amadeuspzs/esp8266-temperature-humidity/analysis/measure-current/mcp-dht.csv

timestamp | current | voltage
52106 | -3.75 | 4176.25
52109 | -2.50 | 4177.50
52111 | -2.50 | 4176.25
52113 | -3.75 | 4176.25
52115 | -5.00 | 4176.25
52117 | -3.75 | 4176.25
52119 | -2.50 | 4176.25
52122 | -3.75 | 4176.25
52124 | -1.25 | 4177.50
52126 | -5.00 | 4176.25
52128 | -3.75 | 4176.25
52130 | -2.50 | 4176.25
52132 | -3.75 | 4176.25
52134 | -3.75 | 4176.25
52137 | -3.75 | 4176.25
52140 | -1.25 | 4176.25
52142 | -3.75 | 4177.50
52144 | -3.75 | 4176.25
52146 | -3.75 | 4176.25
52148 | -5.00 | 4176.25
52151 | -3.75 | 4176.25
52153 | -3.75 | 4176.25
52155 | -3.75 | 4176.25
52157 | -2.50 | 4176.25
52159 | -5.00 | 4176.25
52161 | -3.75 | 4176.25
52164 | -3.75 | 4176.25
52166 | -3.75 | 4177.50
52168 | -3.75 | 4176.25
52170 | -2.50 | 4176.25
52172 | -2.50 | 4175.00
52174 | -2.50 | 4176.25
52177 | -3.75 | 4177.50
52179 | -3.75 | 4175.00
52182 | -3.75 | 4176.25
52184 | -3.75 | 4176.25
52186 | -3.75 | 4176.25
52188 | -2.50 | 4176.25
52190 | -3.75 | 4176.25
52193 | -3.75 | 4176.25
52195 | -3.75 | 4176.25
52197 | -3.75 | 4176.25
52199 | -3.75 | 4176.25
52201 | -5.00 | 4176.25
52203 | -3.75 | 4176.25
52206 | -3.75 | 4176.25
52208 | -3.75 | 4176.25
52210 | -3.75 | 4176.25
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
