amadeuspzs/esp8266-temperature-humidity/analysis/measure-current/mcp-si.csv

timestamp | current | voltage
215763 | -3.75 | 4178.75
215766 | -2.50 | 4178.75
215768 | -3.75 | 4178.75
215770 | -2.50 | 4180.00
215772 | -3.75 | 4178.75
215775 | -2.50 | 4180.00
215777 | -2.50 | 4178.75
215779 | -5.00 | 4178.75
215781 | -3.75 | 4178.75
215783 | -2.50 | 4178.75
215786 | -3.75 | 4178.75
215788 | -2.50 | 4180.00
215790 | -2.50 | 4178.75
215792 | -3.75 | 4180.00
215794 | -3.75 | 4178.75
215797 | -2.50 | 4178.75
215799 | -2.50 | 4178.75
215801 | -2.50 | 4178.75
215803 | -2.50 | 4178.75
215805 | -3.75 | 4178.75
215809 | -3.75 | 4180.00
215811 | -3.75 | 4178.75
215813 | -3.75 | 4178.75
215815 | -3.75 | 4178.75
215817 | -2.50 | 4178.75
215820 | -3.75 | 4180.00
215822 | -3.75 | 4180.00
215824 | -3.75 | 4178.75
215826 | -3.75 | 4178.75
215828 | -2.50 | 4180.00
215831 | -3.75 | 4177.50
215833 | -3.75 | 4178.75
215835 | -3.75 | 4180.00
215837 | -3.75 | 4178.75
215839 | -2.50 | 4178.75
215842 | -2.50 | 4178.75
215844 | -2.50 | 4178.75
215846 | -2.50 | 4178.75
215848 | -2.50 | 4178.75
215851 | -2.50 | 4181.25
215853 | -2.50 | 4180.00
215856 | -2.50 | 4180.00
215858 | -3.75 | 4178.75
215860 | -2.50 | 4178.75
215862 | -3.75 | 4178.75
215864 | -2.50 | 4177.50
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
