amadeuspzs/esp8266-temperature-humidity/analysis/measure-current/slow-auto.csv

Timestamp | Amps
2021-02-22 15:51:02.764359 | 5.64e-09
2021-02-22 15:51:02.764908 | 2.01e-09
2021-02-22 15:51:02.765551 | 5.24e-09
2021-02-22 15:51:02.766239 | 4.84e-09
2021-02-22 15:51:02.766950 | 3.63e-09
2021-02-22 15:51:02.767742 | 4.03e-09
2021-02-22 15:51:02.768414 | 4.84e-09
2021-02-22 15:51:02.769081 | -5.24e-09
2021-02-22 15:51:02.769889 | 2.42e-09
2021-02-22 15:51:02.770635 | 5.64e-09
2021-02-22 15:51:02.771264 | -2.82e-09
2021-02-22 15:51:02.771958 | 2.42e-09
2021-02-22 15:51:02.772755 | 7.25e-09
2021-02-22 15:51:02.773476 | -8.1e-10
2021-02-22 15:51:02.774299 | 1.21e-09
2021-02-22 15:51:02.774881 | 4.43e-09
2021-02-22 15:51:02.775707 | -5.64e-09
2021-02-22 15:51:02.776488 | -8.1e-10
2021-02-22 15:51:02.777055 | 6.04e-09
2021-02-22 15:51:02.777880 | -4.03e-09
2021-02-22 15:51:02.778717 | 8.1e-10
2021-02-22 15:51:02.779432 | 3.63e-09
2021-02-22 15:51:02.780113 | -5.64e-09
2021-02-22 15:51:02.780817 | 5.24e-09
2021-02-22 15:51:02.781465 | 4.03e-09
2021-02-22 15:51:02.782227 | -1.007e-08
2021-02-22 15:51:02.782843 | 3.63e-09
2021-02-22 15:51:02.783751 | 5.24e-09
2021-02-22 15:51:02.784434 | 0.0
2021-02-22 15:51:02.785156 | 3.22e-09
2021-02-22 15:51:02.785728 | 4.84e-09
2021-02-22 15:51:02.786615 | 1.61e-09
2021-02-22 15:51:02.787189 | 5.64e-09
2021-02-22 15:51:02.788029 | 2.42e-09
2021-02-22 15:51:02.788733 | 6.04e-09
2021-02-22 15:51:02.789595 | 0.0
2021-02-22 15:51:02.790233 | 3.22e-09
2021-02-22 15:51:02.791114 | 6.85e-09
2021-02-22 15:51:02.791765 | -4.03e-09
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
2021-02-22 15:51:05.323331 | 0.01491
2021-02-22 15:51:05.324135 | 0.01531
2021-02-22 15:51:05.324833 | 0.01491
2021-02-22 15:51:05.325532 | 0.01491
2021-02-22 15:51:05.326939 | 0.01531
2021-02-22 15:51:05.327389 | 0.01531
2021-02-22 15:51:05.327843 | 0.01531
2021-02-22 15:51:05.328744 | 0.01491
2021-02-22 15:51:05.329244 | 0.01451
2021-02-22 15:51:05.330108 | 0.01491
2021-02-22 15:51:05.330731 | 0.01652
2021-02-22 15:51:05.331535 | 0.02136
2021-02-22 15:51:05.332164 | 0.03707
2021-02-22 15:51:05.333027 | 0.03828
2021-02-22 15:51:05.333577 | 0.04916
2021-02-22 15:51:05.334411 | 0.07374
2021-02-22 15:51:05.335176 | 0.0681
2021-02-22 15:51:05.335839 | 0.07253
2021-02-22 15:51:05.336707 | 0.07333
2021-02-22 15:51:05.337392 | 0.07535
2021-02-22 15:51:05.338033 | 0.07132
2021-02-22 15:51:05.338779 | 0.34773
2021-02-22 15:51:05.339694 | 0.06729
2021-02-22 15:51:05.340247 | 0.06689
2021-02-22 15:51:05.341001 | 0.06366
2021-02-22 15:51:05.341767 | 0.06568
2021-02-22 15:51:05.342472 | 0.06769
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
