amadeuspzs/esp8266-temperature-humidity/analysis/measure-current/slow-ma.csv

Timestamp | Amps
2021-02-22 15:52:27.855331 | 0.0004
2021-02-22 15:52:27.856332 | -0.0004
2021-02-22 15:52:27.856702 | 0.0
2021-02-22 15:52:27.857150 | 0.0004
2021-02-22 15:52:27.857979 | -0.0004
2021-02-22 15:52:27.858691 | -0.0004
2021-02-22 15:52:27.859492 | 0.0
2021-02-22 15:52:27.860437 | -0.00081
2021-02-22 15:52:27.860955 | -0.0004
2021-02-22 15:52:27.862128 | 0.0
2021-02-22 15:52:27.862557 | 0.0
2021-02-22 15:52:27.863056 | -0.0004
2021-02-22 15:52:27.864167 | 0.0
2021-02-22 15:52:27.864671 | 0.0
2021-02-22 15:52:27.865335 | -0.0004
2021-02-22 15:52:27.866077 | 0.0004
2021-02-22 15:52:27.866788 | -0.0004
2021-02-22 15:52:27.867430 | -0.0004
2021-02-22 15:52:27.868183 | 0.0004
2021-02-22 15:52:27.869142 | 0.0
2021-02-22 15:52:27.869662 | -0.00081
2021-02-22 15:52:27.870295 | 0.0
2021-02-22 15:52:27.871127 | 0.0
2021-02-22 15:52:27.871908 | 0.0
2021-02-22 15:52:27.872583 | 0.0004
2021-02-22 15:52:27.873629 | 0.0
2021-02-22 15:52:27.874130 | 0.0
2021-02-22 15:52:27.874679 | 0.0
2021-02-22 15:52:27.875264 | 0.0
2021-02-22 15:52:27.875944 | -0.0004
2021-02-22 15:52:27.876713 | 0.0
2021-02-22 15:52:27.877344 | -0.0004
2021-02-22 15:52:27.878058 | 0.0
2021-02-22 15:52:27.878768 | -0.0004
2021-02-22 15:52:27.879699 | 0.0004
2021-02-22 15:52:27.880220 | 0.0
2021-02-22 15:52:27.881148 | 0.0
2021-02-22 15:52:27.881792 | -0.0004
2021-02-22 15:52:27.882448 | 0.0
2021-02-22 15:52:27.883467 | 0.0
2021-02-22 15:52:27.883954 | 0.0004
2021-02-22 15:52:27.884755 | 0.0004
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
2021-02-22 15:52:29.109295 | 0.0685
2021-02-22 15:52:29.109958 | 0.06769
2021-02-22 15:52:29.111473 | 0.06769
2021-02-22 15:52:29.111878 | 0.0685
2021-02-22 15:52:29.112406 | 0.0689
2021-02-22 15:52:29.113168 | 0.06769
2021-02-22 15:52:29.113895 | 0.0681
2021-02-22 15:52:29.114572 | 0.0689
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
