amadeuspzs/esp8266-temperature-humidity/software/dht22-esp-mains/dht22-esp-mains.ino

/*
 * NodeMCU with DHT22 (mains-powered)
 *
 * MQTT Temperature and Humidity Sensor
 *
 * Designed for integration with HomeAssistant
 *
 */

#include <DHTesp.h>
#include <ESP8266WiFi.h>
#include <PubSubClient.h>

#include "config.h" // WiFi and device settings

WiFiClient espClient;
PubSubClient client(espClient);

DHTesp dht;

float previousTemperature = 0.0;
float previousHumidity = 0.0;
float humidity, temperature, temperatureDifference, humidityDifference;

void setup() {

  // switch on the DHT22 sensor
  pinMode(dhtPowerPin,OUTPUT);
  digitalWrite(dhtPowerPin, HIGH);

  dht.setup(dhtDataPin, DHTesp::DHT22);

  // switch on Serial
  Serial.begin(74880);
  while (!Serial) {}
  Serial.setDebugOutput(true);

  Serial.print("Welcome ");
  Serial.println(device);
  Serial.print("Connecting to ");
  Serial.println(wifi_ssid);

  // switch on WiFi
  WiFi.hostname(wifi_hostname);
  WiFi.begin(wifi_ssid, wifi_password);

  while (WiFi.status() != WL_CONNECTED) {
    delay(100);
    Serial.print(".");
  }

  Serial.println("");
  Serial.println("WiFi connected");
  Serial.println("IP address: ");
  Serial.println(WiFi.localIP());

  // configure MQTT server
  client.setServer(mqtt_server, 1883);

} // end setup

void loop() {

  // read latest sensors
  humidity = dht.getHumidity();
  temperature = dht.getTemperature();

  Serial.print("Previous temperature (C): ");
  Serial.println(previousTemperature);
  Serial.print("Current temperature (C): ");
  Serial.println(temperature);
  Serial.print("Previous humidity (%): ");
  Serial.println(previousHumidity);
  Serial.print("Current humidity (%): ");
  Serial.println(humidity);

  // calculate difference from last reading
  temperatureDifference = fabs(previousTemperature - temperature);
  humidityDifference = fabs(previousHumidity - humidity);

  Serial.print("Temperature difference (C): ");
  Serial.println(temperatureDifference);
  Serial.print("Humidity difference (%): ");
  Serial.println(humidityDifference);

  // connect to MQTT server
  if (!client.connected()) {
    Serial.print("Attempting MQTT connection...");
    if (client.connect("ESP8266Client")) {
      Serial.println("connected");
    } else {
      Serial.print("failed, rc=");
      Serial.print(client.state());
      Serial.println(" try again in 5 seconds");
      // Wait 5 seconds before retrying
      delay(5000);
    }
  }

  // only publish new reading if outside repeatability range
  if (temperatureDifference >= dhtTemperatureChangeThreshold) {
    Serial.println("Temperature change detected - publishing");
    if (isnan(temperature)) {
      Serial.println("NaN detected on temperature, skipping");
    } else {
      client.publish(temperature_topic, String(temperature).c_str(), true);
      previousTemperature = temperature;
    } // end if NaN
  } else {
    Serial.println("No significant temperature change detected - skipping");
  }

  if (humidityDifference >= dhtHumidityChangeThreshold) {
    Serial.println("Humidity change detected - publishing");
    if (isnan(humidity)) {
      Serial.println("NaN detected on humidity, skipping");
    } else {
      client.publish(humidity_topic, String(humidity).c_str(), true);
      previousHumidity = humidity;
    } // end if NaN
  } else {
    Serial.println("No significant humidity change detected - skipping");
  }

  // drop into next reporting cycle
  Serial.println("Waiting for next reporting cycle...");
  Serial.println();
  delay(polling_ms);

} // end loop
